tigmit/TIGMIT-NEKO-BOARD/Documentation/miscFiles/neopixel miniE.png

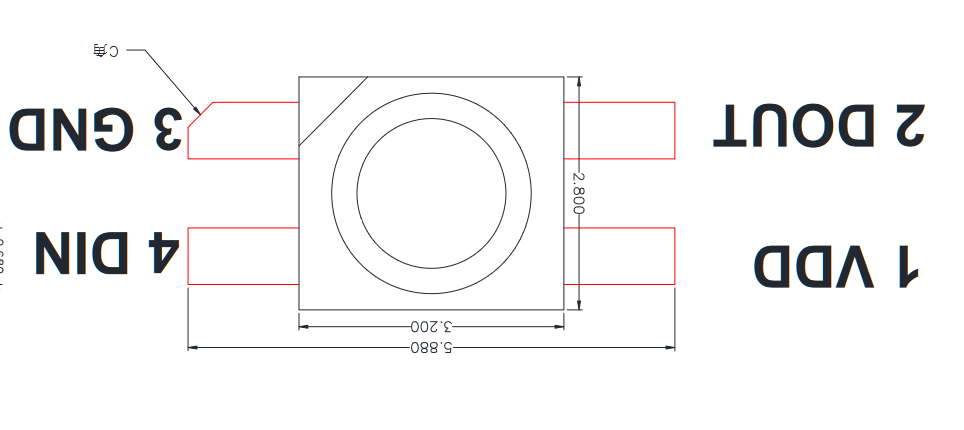
Documentation/miscFiles/neopixel miniE.png
