tigmit/TIGMIT-NEKO-BOARD/Documentation/miscFiles/Screenshot 2024-06-25 231453.png

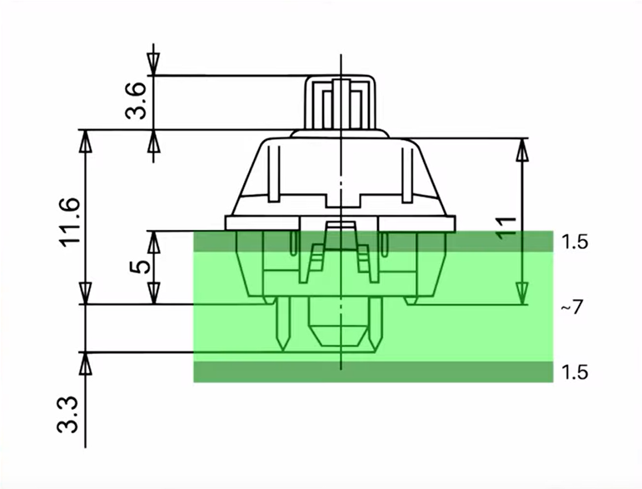
Documentation/miscFiles/Screenshot 2024-06-25 231453.png
