tigmit/TIGMIT-NEKO-BOARD/PNGs/DSPwallpapers/mainScreen.png

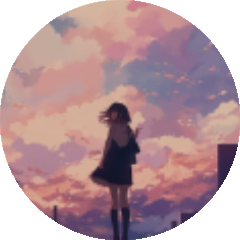
PNGs/DSPwallpapers/mainScreen.png
