tigmit/TIGMIT-NEKO-BOARD/PNGs/DSPwallpapers/wallpaper1.png

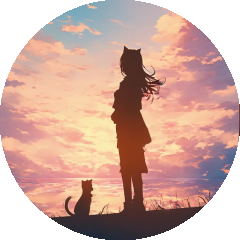
PNGs/DSPwallpapers/wallpaper1.png
