tigmit/TIGMIT-NEKO-BOARD/PNGs/DSPwallpapers/wallpaper2blank.png

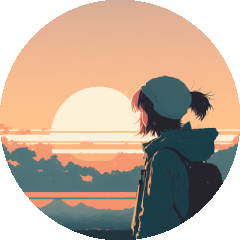
PNGs/DSPwallpapers/wallpaper2blank.png
