tigmit/TIGMIT-NEKO-BOARD/PNGs/DSPwallpapers/wallpaper240X240.png

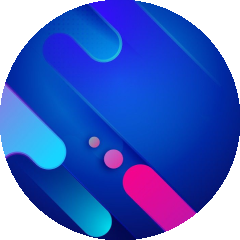
PNGs/DSPwallpapers/wallpaper240X240.png
