tigmit/TIGMIT-NEKO-BOARD/PNGs/shift registers.png

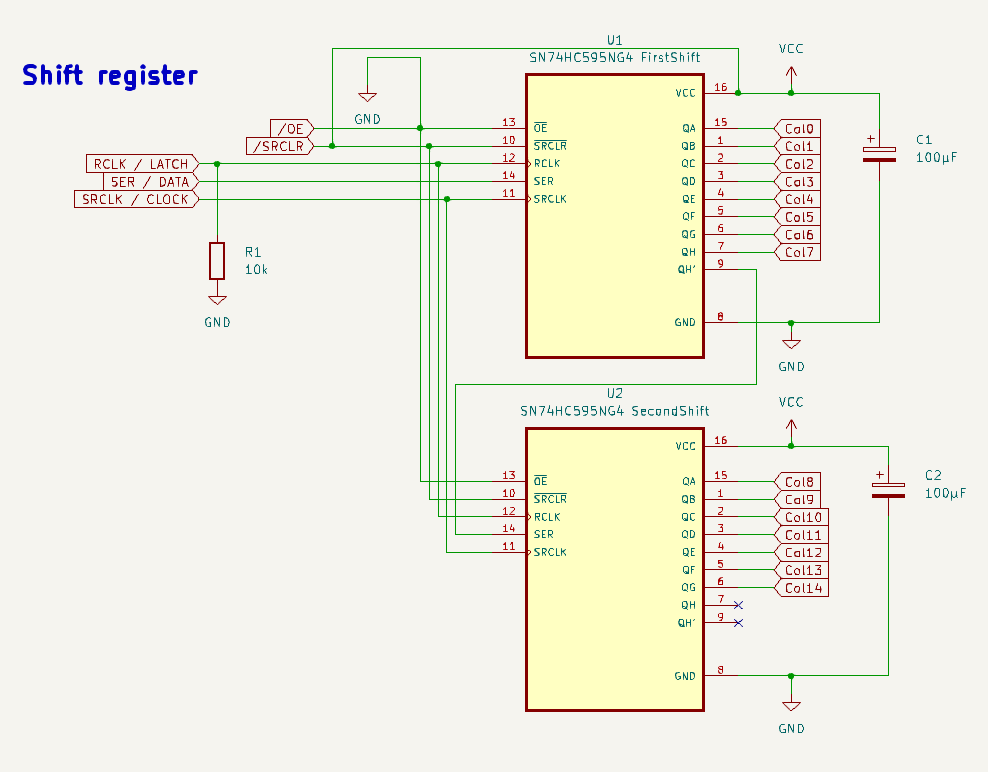
PNGs/shift registers.png
