tigmit/TIGMIT-NEKO-BOARD/PNGs/tigmit Neco board back view.png

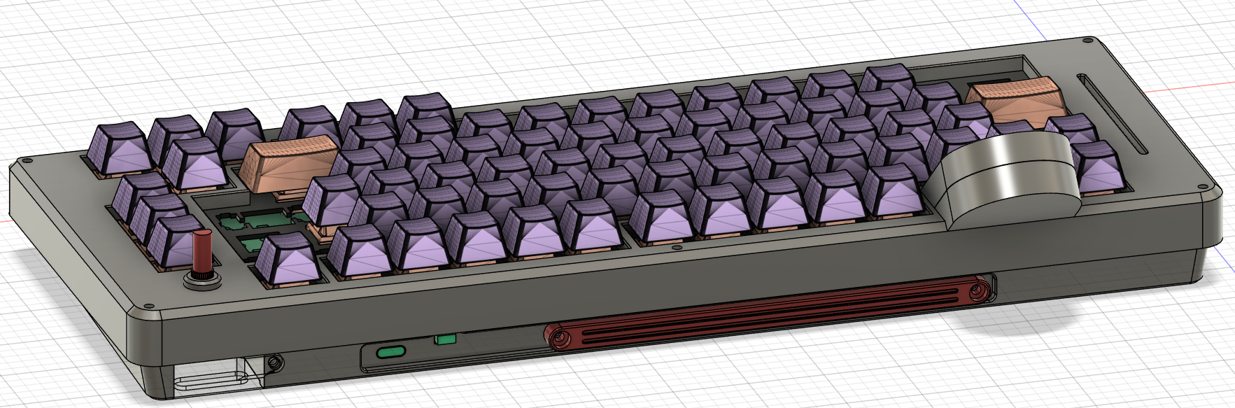
PNGs/tigmit Neco board back view.png
