tigmit/TIGMIT-NEKO-BOARD/PNGs/tigmit Neco board bottom view.png

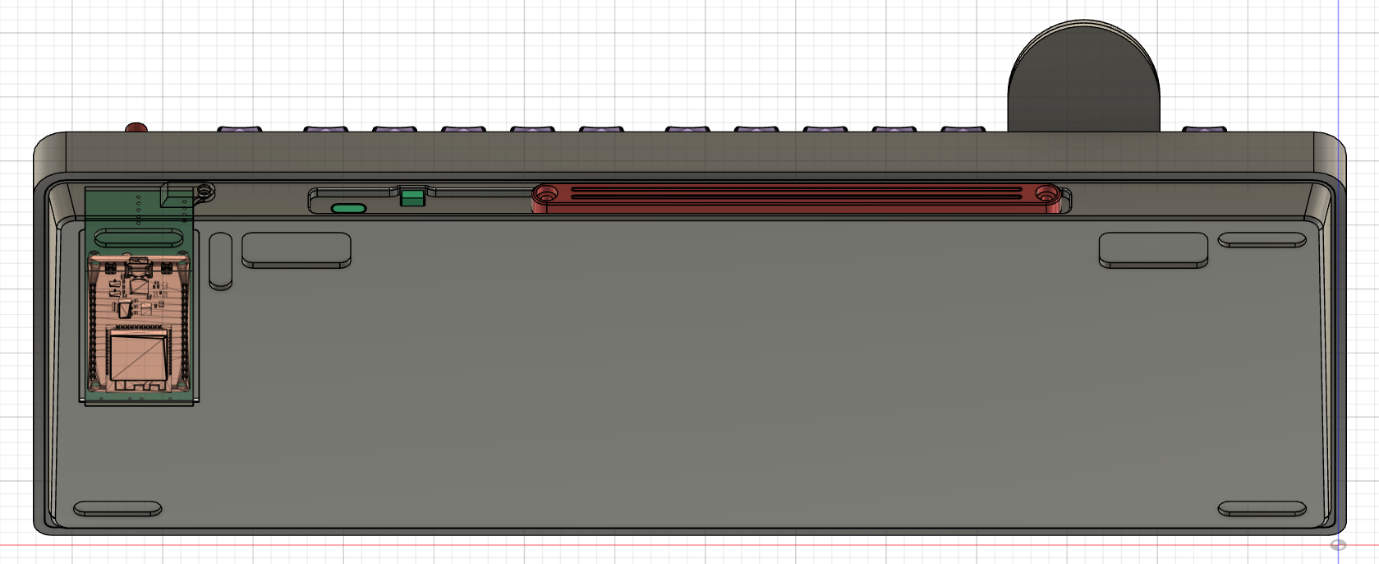
PNGs/tigmit Neco board bottom view.png
