tigmit/TIGMIT-NEKO-BOARD/include/Model.hpp

/**
 * main.cpp
 * brief   : main compilation unit containing loop and setup
 * created : 25.05.2024
 * creator : @tigmit Licence : opensource
 */
#pragma once

#include "BatteryHandler.hpp"
#include "DisplayHandler.hpp"
#include "EncoderHandler.hpp"
#include "KeyBoardHandler.hpp"
#include "RgbHandler.hpp"
#include "ShiftRegisterHandler.hpp"
#include "SliderHandler.hpp"

ShiftRegisterHandler srHandler;
KeyboardHandler kbdHandler(&srHandler);
BatteryHandler batHandler;
EncoderHandler encHandler;
RgbHandler rgbHandler;
SliderHandler sliderHandler;
DisplayHandler dspHandler(&batHandler, &kbdHandler);
